RazMake/PowerDelayDevice/Photos/image001.jpg

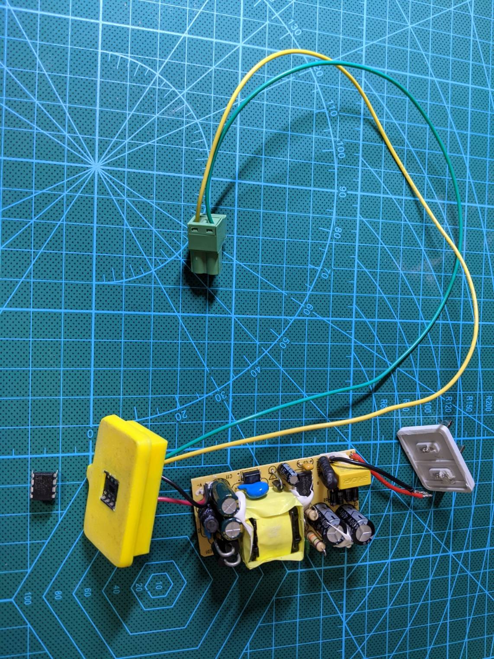
Photos/image001.jpg
