RazMake/PowerDelayDevice/Photos/image002.jpg

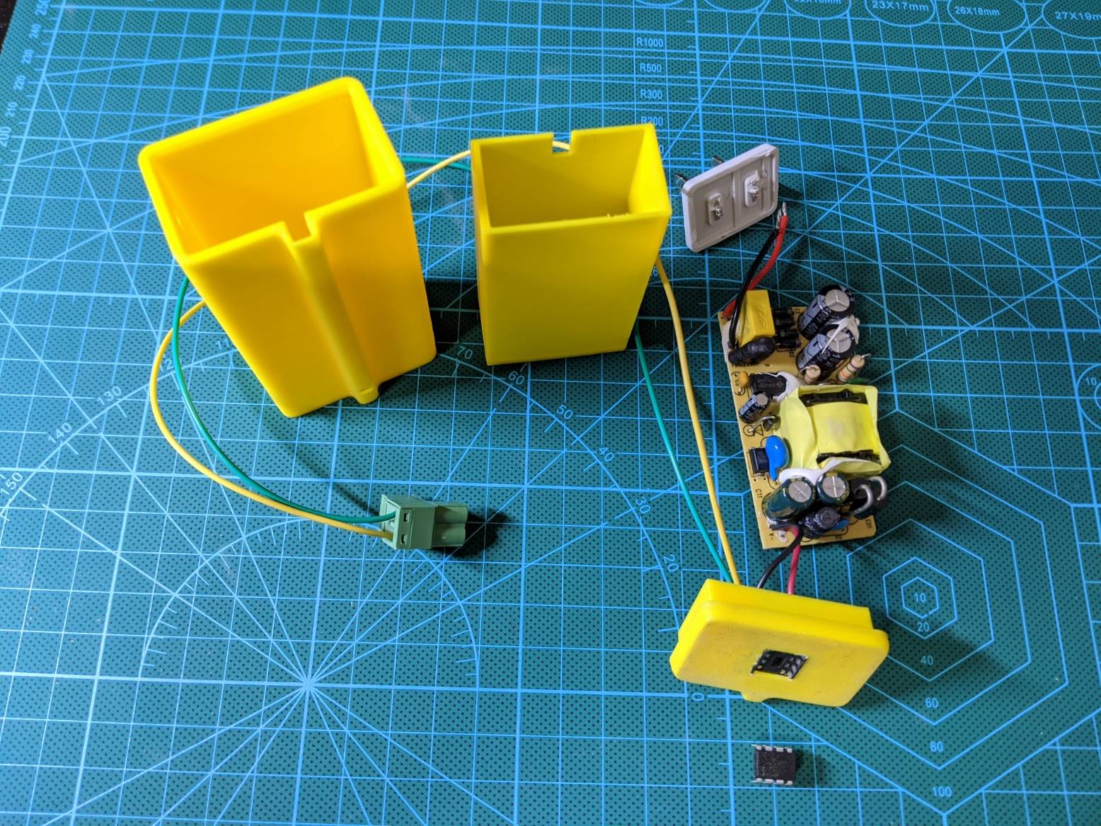
Photos/image002.jpg
