RazMake/PowerDelayDevice/Photos/image003.jpg

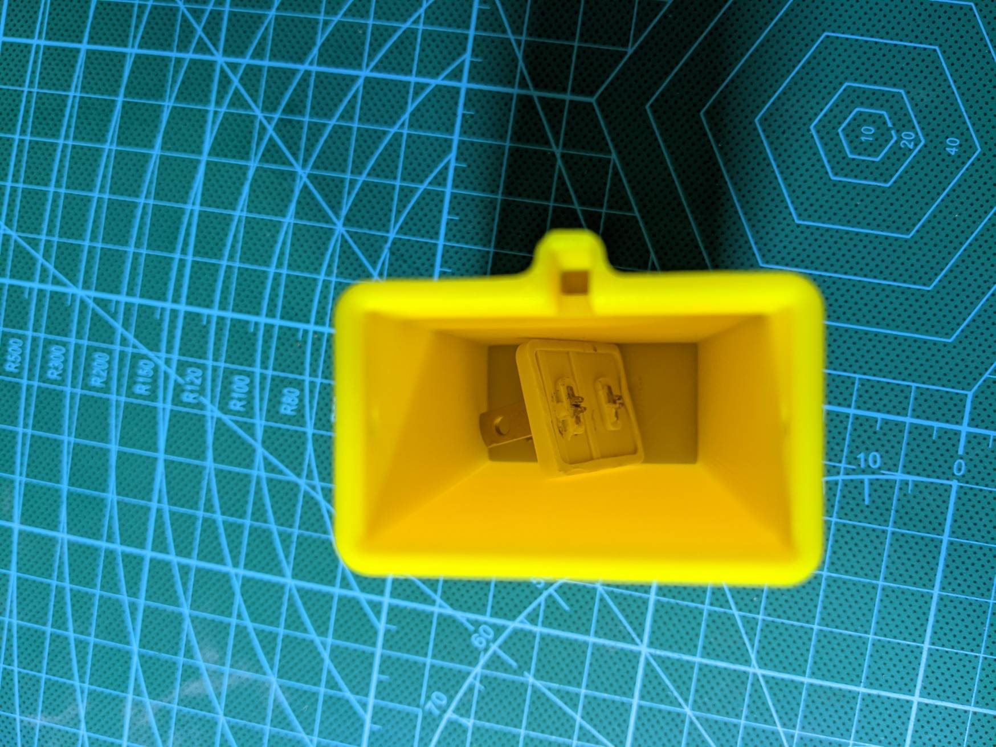
Photos/image003.jpg
