RazMake/PowerDelayDevice/Photos/image004.jpg

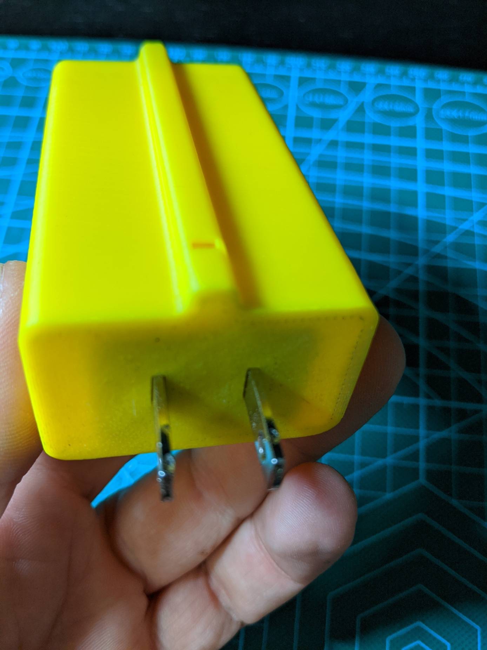
Photos/image004.jpg
