RazMake/PowerDelayDevice/Photos/image005.jpg

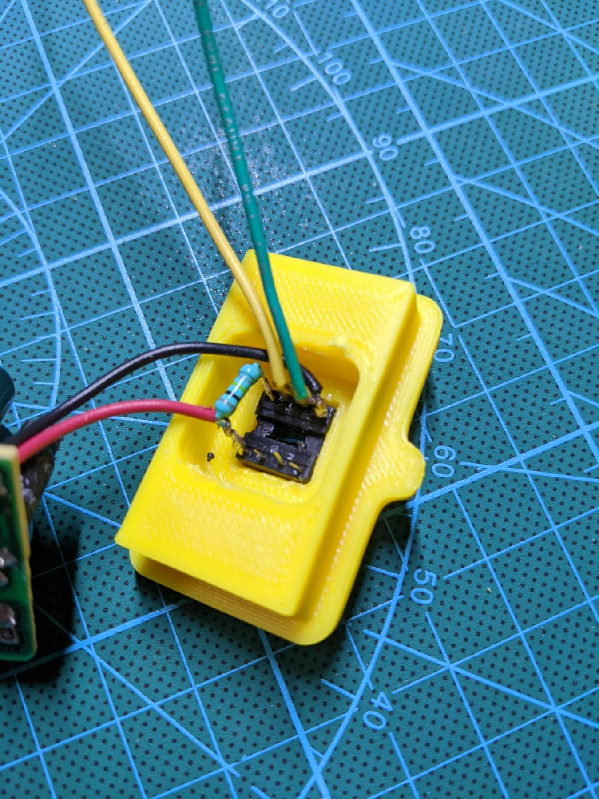
Photos/image005.jpg
