RazMake/PowerDelayDevice/Photos/image006.jpg

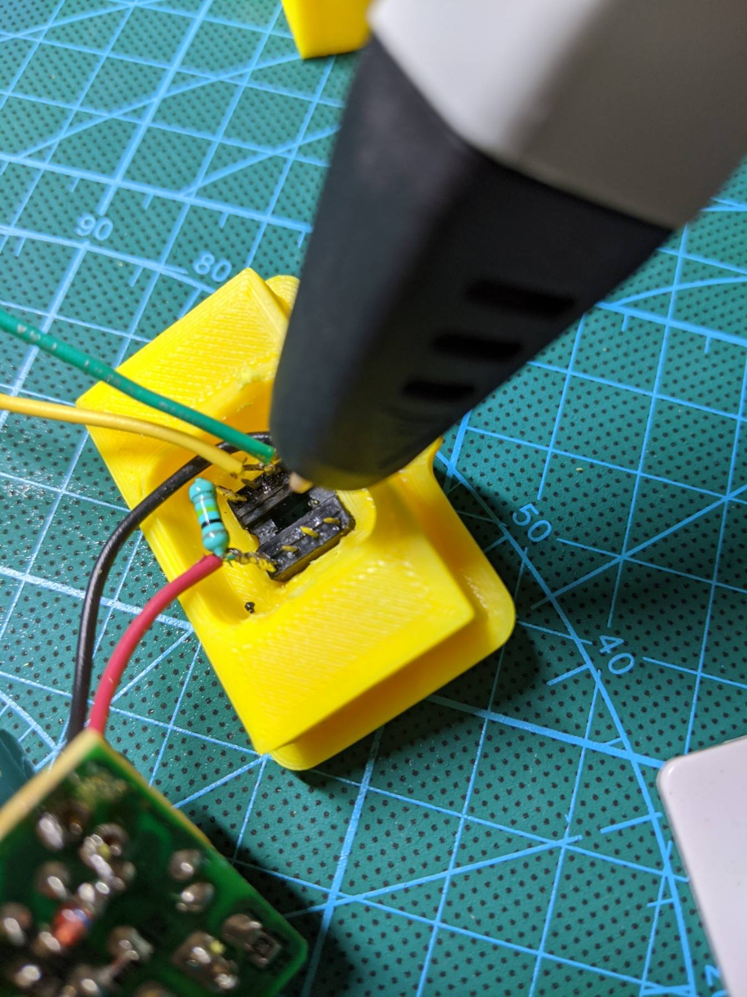
Photos/image006.jpg
